breadbee/breadbee/addons/wifi/output/wifi-usb-breakout-brd-600dpi.png

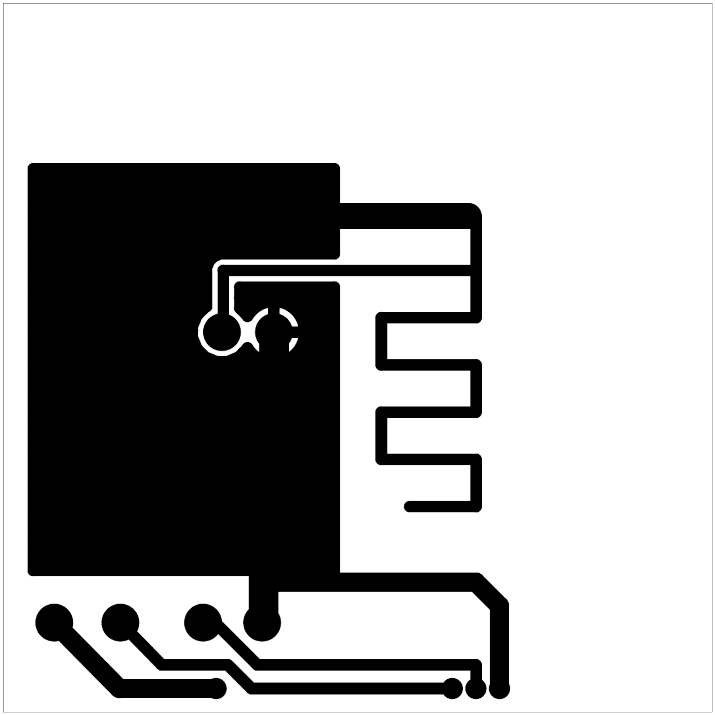
addons/wifi/output/wifi-usb-breakout-brd-600dpi.png
