breadbee/breadbee/addons/wifi/photos/IMG_0371cs2.JPG

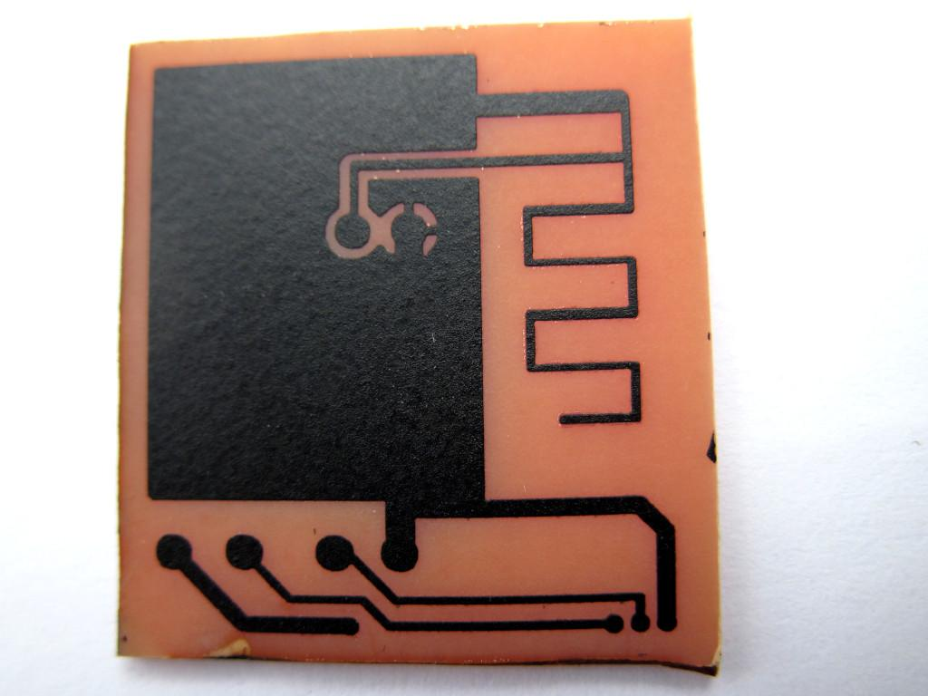
addons/wifi/photos/IMG_0371cs2.JPG
