breadbee/breadbee/addons/wifi/photos/IMG_0374cs2.JPG

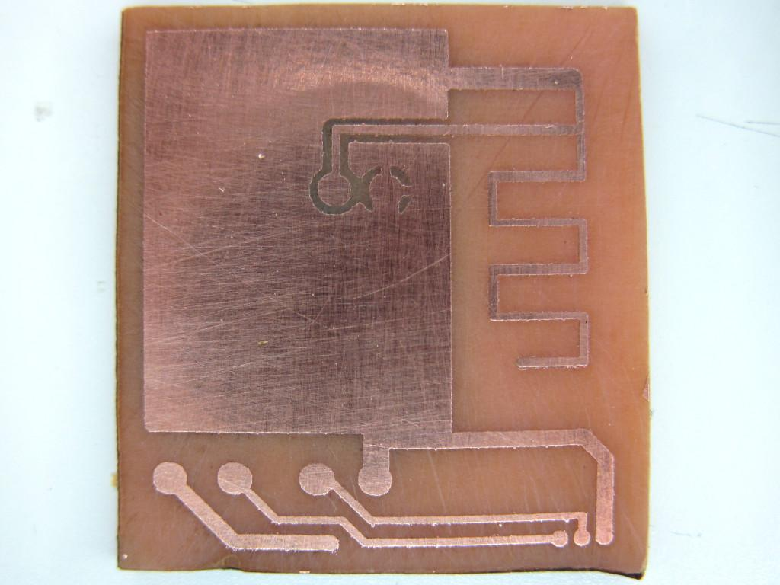
addons/wifi/photos/IMG_0374cs2.JPG
