breadbee/breadbee/renders/breadbee_back.png

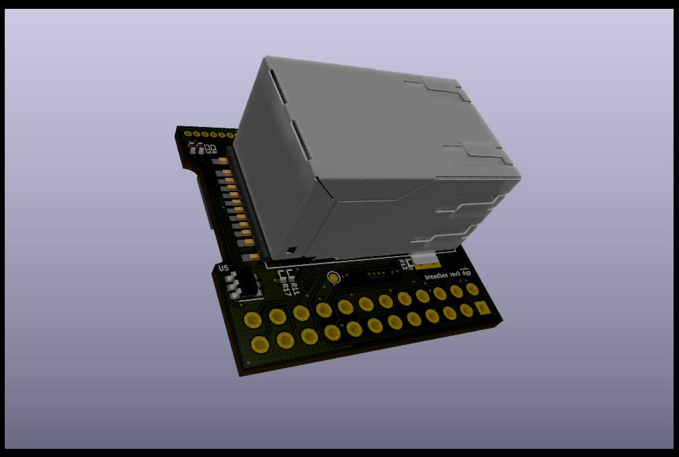
renders/breadbee_back.png
